JayMcGee/Aquarius/src/build_src/drivers/I2C/Atlas_I2C_DO.h

/**
 * @file   Atlas_I2C_DO.h
 * @author Jean-Philippe Fournier and Jean-Pascal McGee
 * @date   Febuary 18 2015
 * @brief  Contains a child of Atlas_I2C with the DO particularities
 */

#include "../../commun.h"
#include <iostream>
#include <stdlib.h> 
#include <stdio.h>   
#include "../../../include/blacklib/BlackLib.h"
#include "../../../include/blacklib/BlackI2C.h"
#include "Atlas_I2C.h"

//Custom DO commands
#define DO_COMMAND_P "P"
#define DO_COMMAND_S "S"
#define DO_COMMAND_O "O"

//DO calibration parameters
#define DO_CAL_AIR "Oxy"
#define DO_CAL_0_O "0"

#define DO_COMMAND_P_DELAY 3
#define DO_COMMAND_S_DELAY 3
#define DO_COMMAND_O_DELAY 3

#define DO_COMPENSATION_PRESSURE "Pressure compensation at : "
#define DO_COMPENSATION_SET_PRESSURE "Pressure compensation now at : "

#define DO_COMPENSATION_SALINITY "Pressure compensation at : "
#define DO_COMPENSATION_SET_SALINITY "Pressure compensation now at : "

#define DO_OUTPUT_SET_AT "Output string set with : "
#define DO_OUTPUT_IS_AT "Output string is currently at : "

//Number of data outputted by the device
#define ATLAS_DO_DATA_QTY 2
#define ATLAS_DO_DATA_1 "%"
#define ATLAS_DO_DATA_2 "DO"

namespace aquarius
{
	//Inherits a base Atlas_I2C device
	class Atlas_I2C_DO : public Atlas_I2C
	{
		public:
			//Contains the name of all datas outputted by the device
		    static const string dataName[ATLAS_DO_DATA_QTY];
		    
		    /**
		    * Main constructor that builds by calling the parent constructor
		    * @param deviceName 
		    * @param i2c
		    */
			Atlas_I2C_DO(string deviceName, BlackI2C * i2c)  : Atlas_I2C(deviceName,i2c){};
			
			/**
			 * @brief Calibrates the device
			 * 
			 * @param parameter calibration parameter (query, level)
			 * @param value value for calibration, NO_CALIBRATION_VALUE is default
			 * 
			 * @return I2C commande result code
			 */
			int command_Calibration(string parameter, string value = NO_CALIBRATION_VALUE);
			
			/**
			 * @brief Outputs a reading
			 * @details Using the common aquarius output system, read and output the sensor
			 * @return I2C commande result code
			 */
		    int command_Reading();
			
			/**
			 * @brief Changes the output string from the device
			 * @details Use with caution, can alter the reading functions accuracy
			 * 
			 * @param parameter Command parameter
			 * @param enable Enable/Disable the output
			 * 
			 * @return I2C commande result code
			 */
			int command_Output_String_Config(string parameter, string enable = NO_CALIBRATION_VALUE);
			
			/**
			 * @brief Pressure compensation command
			 * @details Set the pressure compensation on the device
			 * 
			 * @param parameter The pressure parameter or query parameter
			 * @return I2C commande result code
			 */
			int command_Pressure(string parameter);
			
			/**
			 * @brief Salinity compensation commad
			 * @details Set the salinity compensation on the device
			 * 
			 * @param parameter The salinity parameter or query parameter
			 * @return I2C commande result code
			 */
			int command_Salinity(string parameter);			
	};
}
